ttosu25/SG-3/tr/experiments/current_source_circuit/MHCP.asc

Load: res; 344.75
R1: res; {R}
R2: res; {R}
R3: res; {RTOP}
R4: res; {RTOP}
U1: OP177A
V1: voltage; SINE(0 5 400 1n 1n)
V3: voltage; 5
V4: voltage; -5
Named nets: 0
.param R=50 RTOP=200 SHUNT=1k
.tran 20m
