ttosu25/SG-3/tr/experiments/ina/instrumentation_amp.asc

R1: res; {R_con}
R2: res; {R_buff}
R3: res; {R_buff}
R4: res; {R}
R5: res; {R}
R6: res; {R}
R7: res; {R}
U1: OP177A
U2: OP177A
U3: OP177A
V1: voltage; 10
V2: voltage; -10
V3: voltage; -10
V4: voltage; 10
Vin: voltage; SINE(0 15m 400 1n 1n)
Named nets: 0, Vout
.param R=1k R_con=1k R_buff=47k
.tran 20m
WSB_ref
