ttosu25/SG-3/tr/experiments/sync_demod/demodulator_besselLPF.asc

ac_current_source_voltage: voltage; SINE(0 2.1 400 1n 1n)
C1: cap; 1µ
C2: cap; 1µ
C3: cap; 1.96µ
ina_out: voltage; SINE(0 {v_sig} 400 1n 1n)
R1: res; 1.5k
R2: res; 825
R3: res; 1.15k
U1: AD630
U2: opamp2; OPAx187
U4: opamp2; OPAx187
V1: voltage; 5
V2: voltage; -5
V3: voltage; -5
V4: voltage; 5
Named nets: 0, demod
.tran 100m
.include OPAx187.lib
.step param v_sig 1 2
