ttosu25/SG-3/tr/experiments/sync_demod/logsum.asc

D1: diode; 1N4148
D2: diode; 1N4148
R1: res; {REXP}
R2: res; {REXP}
R3: res; {REXP}
R4: res; {REXP}
R5: res; {REXP}
R6: res; {REXP}
R7: res; {REXP}
R8: res; {REXP}
R9: res; {REXP}
R10: res; {REXP}
R11: res; {REXP}
U1: OP177A
U2: OP177A
U3: OP177A
U4: OP177A
U5: OP177A
U6: OP177A
V1: voltage; 10
V2: voltage; -10
Vin: voltage; SINE(1.5 1.5 400 1n 1n)
Vref: voltage; SINE(1 1 400 1n 1n)
Named nets: 0, sum
.param REXP=10k
.tran 20m
