ttosu25/SG-3/tr/experiments/sync_demod/multIC_demod.asc

C1: cap; 1µ
R1: res; 20k
U1: AD633
V1: voltage; SINE(0 {sig_am} 400 1n 1n)
V2: voltage; SINE(0 1 400 1n 1n)
V3: voltage; 15
V4: voltage; -15
Named nets: 0, Demod
.tran 20m
.include AD633.cir
.step param sig_am list 1 3 5 7 9 11 13 15
