ttosu25/SG-3/tr/experiments/sync_demod/multiplier.asc

D1: diode; 1N4148
D2: diode; 1N4148
D3: diode; 1N4148
D4: diode; 1N4148
R1: res; {REXP}
R2: res; {REXP}
R3: res; {REXP}
R4: res; {REXP}
R5: res; {REXP}
R6: res; {REXP}
R7: res; {REXP}
R8: res; {REXP}
R9: res; {REXP}
R10: res; {REXP}
R11: res; {REXP}
R12: res; {REXP}
R13: res; {REXP}
R14: res; {REXP}
R15: res; {REXP}
R16: res; {REXP}
R17: res; {REXP}
R18: res; {REXP}
R19: res; {REXP}
R20: res; {REXP}
U1: OP177A
U2: OP177A
U3: OP177A
U4: OP177A
U5: OP177A
U6: OP177A
U7: OP177A
U8: OP177A
U9: OP177A
U10: OP177A
U11: OP177A
V1: voltage; 10
V2: voltage; -10
V3: voltage; 1
Vin: voltage; SINE(1.5 1.5 400 1n 1n)
Vref: voltage; SINE(1 1 400 1n 1n)
Named nets: 0, mult
.param REXP=10k
.tran 20m
