ttosu25/SG-3/tr/experiments/wheatstone_bridge/wheatstone_bridge.asc

I1: current; SINE(0 5.3m 400 1n 1n)
R1: res; 350
R2: res; 350
R3: res; 350
R+Sensor: res; {Rvar}
Named nets: 0, Vb, Va
.param Rvar=350
.tran 20m
